Christian-Loja/Dise-o-PCB-SMD-para-Sistema-de-registro-continuo-de-se-ales-acelerom-tricas/images_pcb_layers/bottom_route.png

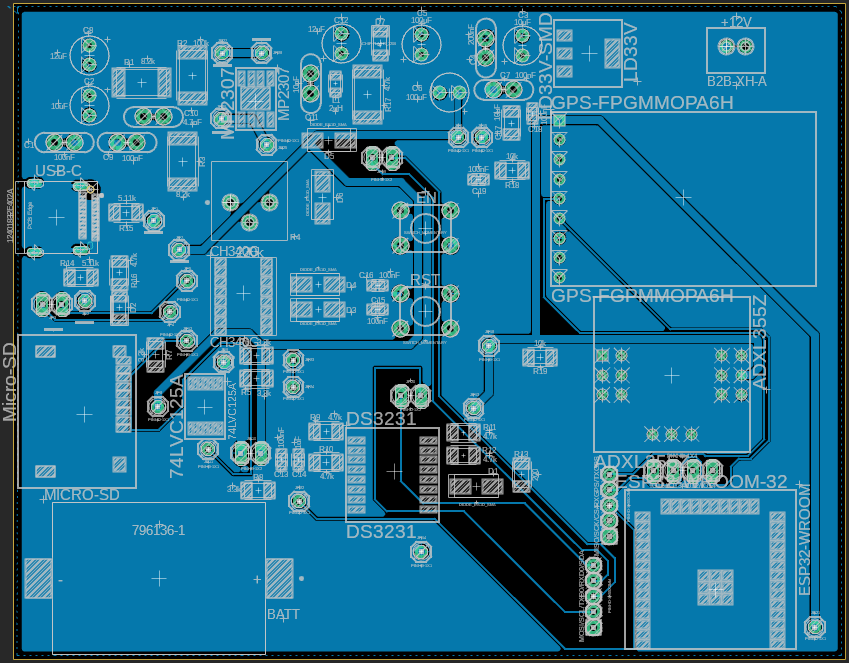
images_pcb_layers/bottom_route.png
