Christian-Loja/Dise-o-PCB-SMD-para-Sistema-de-registro-continuo-de-se-ales-acelerom-tricas/images_pcb_layers/top_bottom_route.png

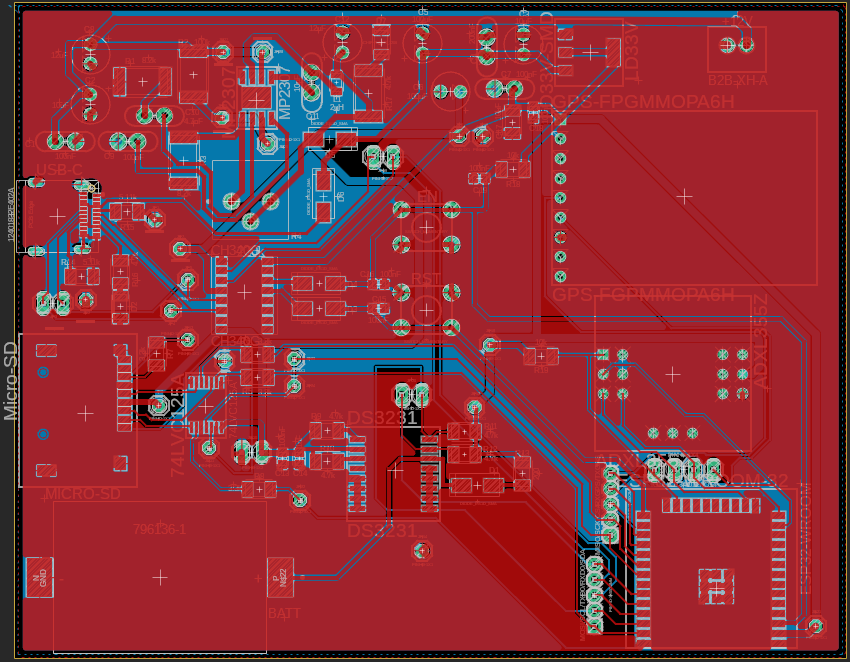
images_pcb_layers/top_bottom_route.png
