Christian-Loja/Dise-o-PCB-SMD-para-Sistema-de-registro-continuo-de-se-ales-acelerom-tricas/images_schematic/ERC.png

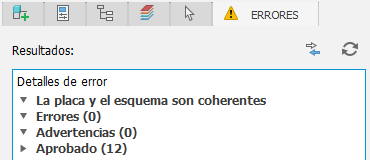
images_schematic/ERC.png
