Christian-Loja/Dise-o-PCB-SMD-para-Sistema-de-registro-continuo-de-se-ales-acelerom-tricas/images_pcb_layers/pads_components.png

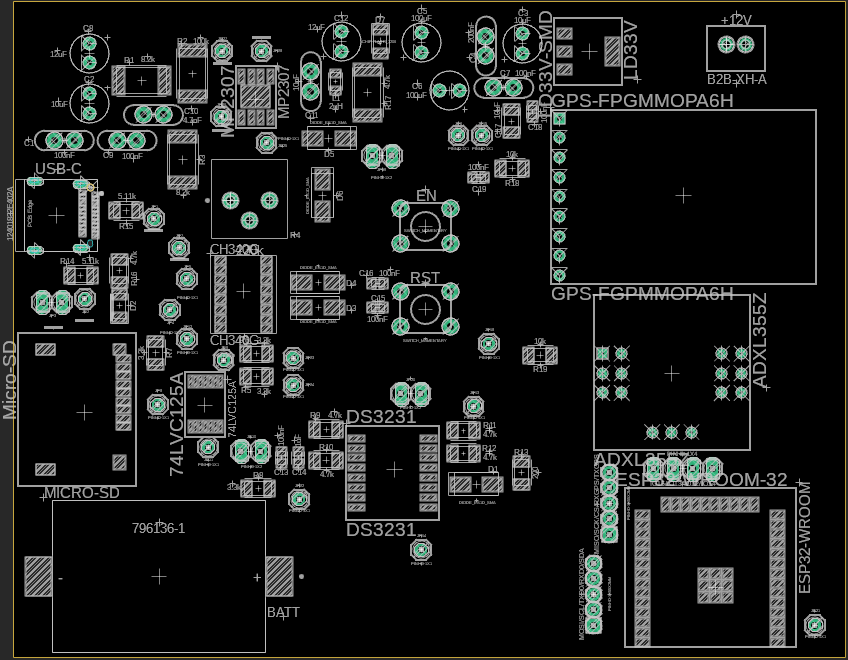
images_pcb_layers/pads_components.png
